amera64/bambu_dashboard_v2/Config.h

#pragma once

// Display pins

#define TFT_SCLK 12
#define TFT_MOSI 11
#define TFT_MISO 13
#define TFT_CS   10
#define TFT_DC   46
#define TFT_BL   45

#define BBL_PRINTER_IP "192.168.1.215"
#define BBL_USERNAME "bblp"
#define BBL_ACCESS_CODE "your_code_here"
