amera64/bambu_dashboard_v2/Icons.cpp

#include "Icons.h"

#include "Display.h"
#include "Theme.h"











void drawBedIcon(int x, int y, uint16_t color)
{
    // print bed surface
    lcd.fillRoundRect(
        x,
        y + 14,
        24,
        5,
        2,
        color
    );

    // supports
    lcd.drawLine(
        x + 4,
        y + 19,
        x + 4,
        y + 24,
        color
    );

    lcd.drawLine(
        x + 20,
        y + 19,
        x + 20,
        y + 24,
        color
    );

    // top layer
    lcd.drawLine(
        x + 2,
        y + 12,
        x + 22,
        y + 12,
        color
    );
}

void drawPauseIcon(int x, int y, uint16_t color)
{
    lcd.fillRoundRect(
        x,
        y,
        7,
        24,
        2,
        color
    );

    lcd.fillRoundRect(
        x + 14,
        y,
        7,
        24,
        2,
        color
    );
}


void drawPlayIcon(int x, int y, uint16_t color)
{
    lcd.fillTriangle(
        x,
        y,
        x,
        y + 24,
        x + 22,
        y + 12,
        color
    );
}


void drawStopIcon(int x, int y, uint16_t color)
{
    lcd.fillRoundRect(
        x,
        y,
        24,
        24,
        3,
        color
    );
}


void drawLightIcon(
    int x,
    int y,
    uint16_t color
)
{
    // Bulb globe
    lcd.fillCircle(
        x,
        y,
        5,
        color
    );

    // Neck
    lcd.fillRoundRect(
        x - 3,
        y + 5,
        6,
        4,
        1,
        color
    );

    // Base
    lcd.drawLine(
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
    int y,
    uint16_t color
)
{
    lcd.drawCircle(
        x,
        y,
        7,
        color
    );

    lcd.fillCircle(
        x,
        y,
        3,
        color
    );

    // Gear teeth
    lcd.fillRect(
        x - 2,
        y - 12,
        4,
        4,
        color
    );

    lcd.fillRect(
        x - 2,
        y + 8,
        4,
        4,
        color
    );

    lcd.fillRect(
        x - 12,
        y - 2,
        4,
        4,
        color
    );

    lcd.fillRect(
        x + 8,
        y - 2,
        4,
        4,
        color
    );

    lcd.fillRect(
        x - 9,
        y - 9,
        4,
        4,
        color
    );

    lcd.fillRect(
        x + 5,
        y - 9,
        4,
        4,
        color
    );

    lcd.fillRect(
        x - 9,
        y + 5,
        4,
        4,
        color
    );

    lcd.fillRect(
        x + 5,
        y + 5,
        4,
        4,
        color
    );
}
