amera64/bambu_dashboard_v2/Layout.h

#pragma once

namespace Layout
{
    // Screen
    constexpr int SCREEN_WIDTH = 320;
    constexpr int SCREEN_HEIGHT = 240;

    // Header
    constexpr int HEADER_X = 5;
    constexpr int HEADER_Y = 5;
    constexpr int HEADER_WIDTH = 310;
    constexpr int HEADER_HEIGHT = 45;
    constexpr int HEADER_RADIUS = 8;

    // Page content
    constexpr int CONTENT_TOP = 55;

    // Navigation
    constexpr int NAV_X = 5;
    constexpr int NAV_Y = 205;
    constexpr int NAV_WIDTH = 310;
    constexpr int NAV_HEIGHT = 30;
    constexpr int NAV_RADIUS = 8;

    // Home page
    constexpr int PROGRESS_X = 10;
    constexpr int PROGRESS_Y = 55;
    constexpr int PROGRESS_WIDTH = 145;
    constexpr int PROGRESS_HEIGHT = 110;

    constexpr int NOZZLE_X = 165;
    constexpr int NOZZLE_Y = 55;
    constexpr int NOZZLE_WIDTH = 145;
    constexpr int NOZZLE_HEIGHT = 50;

    constexpr int BED_X = 165;
    constexpr int BED_Y = 115;
    constexpr int BED_WIDTH = 145;
    constexpr int BED_HEIGHT = 50;

    constexpr int BOTTOM_INFO_X = 10;
    constexpr int BOTTOM_INFO_Y = 168;
    constexpr int BOTTOM_INFO_WIDTH = 300;
    constexpr int BOTTOM_INFO_HEIGHT = 33;

    // Shared card appearance
    constexpr int CARD_RADIUS = 8;
}
