amera64/bambu_dashboard_v2/Theme.h

#pragma once

// Background
#define COLOR_BG       0x18C3

// Cards
#define COLOR_CARD     0x2945

// Borders
#define COLOR_BORDER   0x5ACB

// Text
#define COLOR_TEXT     TFT_WHITE
#define COLOR_DIM      0x8410

// Accent
#define COLOR_ACCENT   0x05E0

// Warning
#define COLOR_WARN     TFT_YELLOW

// Error
#define COLOR_ERROR    TFT_RED

#define COLOR_PANEL      0x2104
#define COLOR_ACCENT2    0x07FF
#define COLOR_GREEN      0x05E0
#define COLOR_BLUE       0x18d3
#define COLOR_GREY       0x7bf0
#define COLOR_ORANGE     0xFD20
#define COLOR_RED        0xF800
#define COLOR_GRAY_TEXT  0xBDF7
