amera64/bambu_dashboard_v2/UIUpdateFlags.h

#pragma once

struct UIUpdateFlags
{
    volatile bool header;
    volatile bool progress;
    volatile bool progressStatus;
    volatile bool nozzle;
    volatile bool bed;
    volatile bool bottomInfo;
    volatile bool ams;
    volatile bool controls;
    volatile bool system;
    volatile bool tempNozzle;
    volatile bool tempBed;
    volatile bool tempChamber;

};

extern UIUpdateFlags uiUpdates;



void markAllUIUpdates();
void clearAllUIUpdates();
